I-A-M-M-O-S/AVA/CAD/KiCad/AVA/FAB/PDF/AVA-B_Cu.png

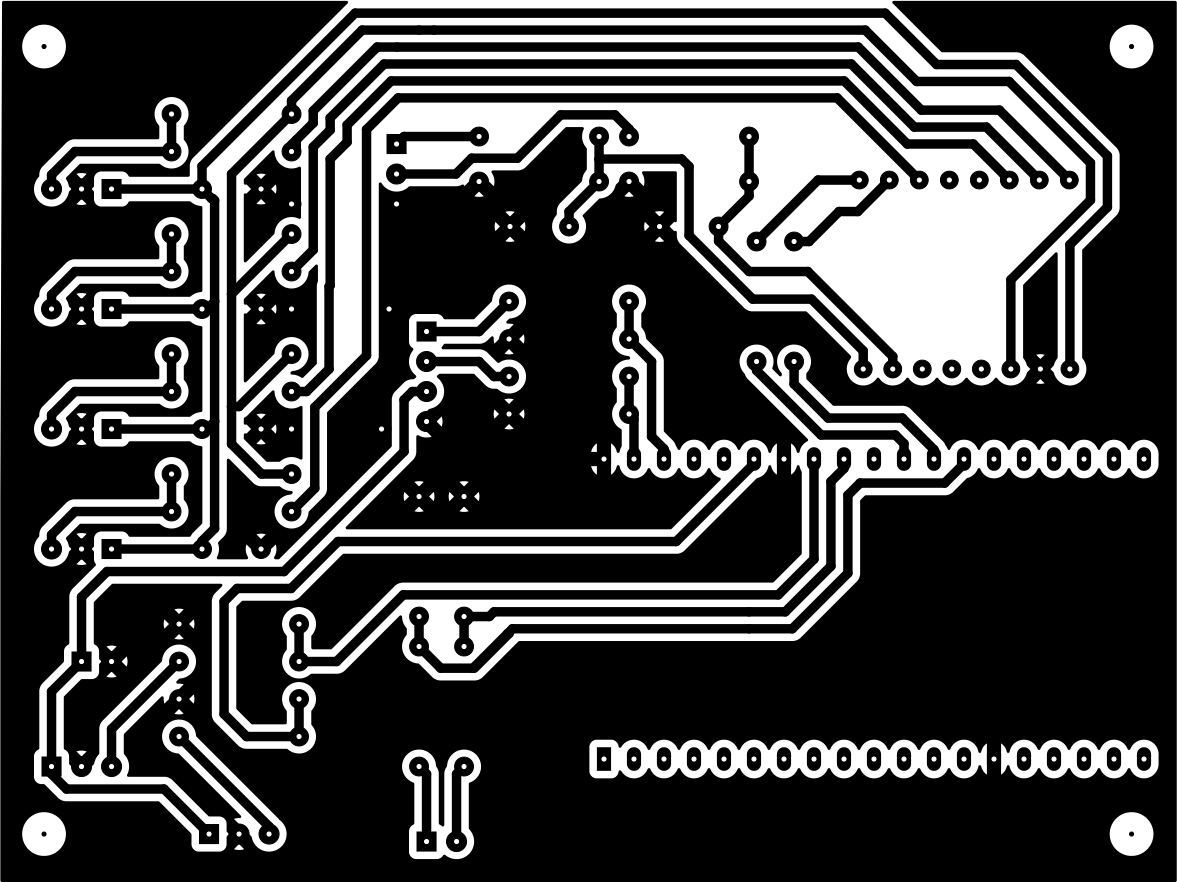
CAD/KiCad/AVA/FAB/PDF/AVA-B_Cu.png
