I-A-M-M-O-S/AVA/CAD/KiCad/AVA/FAB/SVG/AVA-F_Cu.png

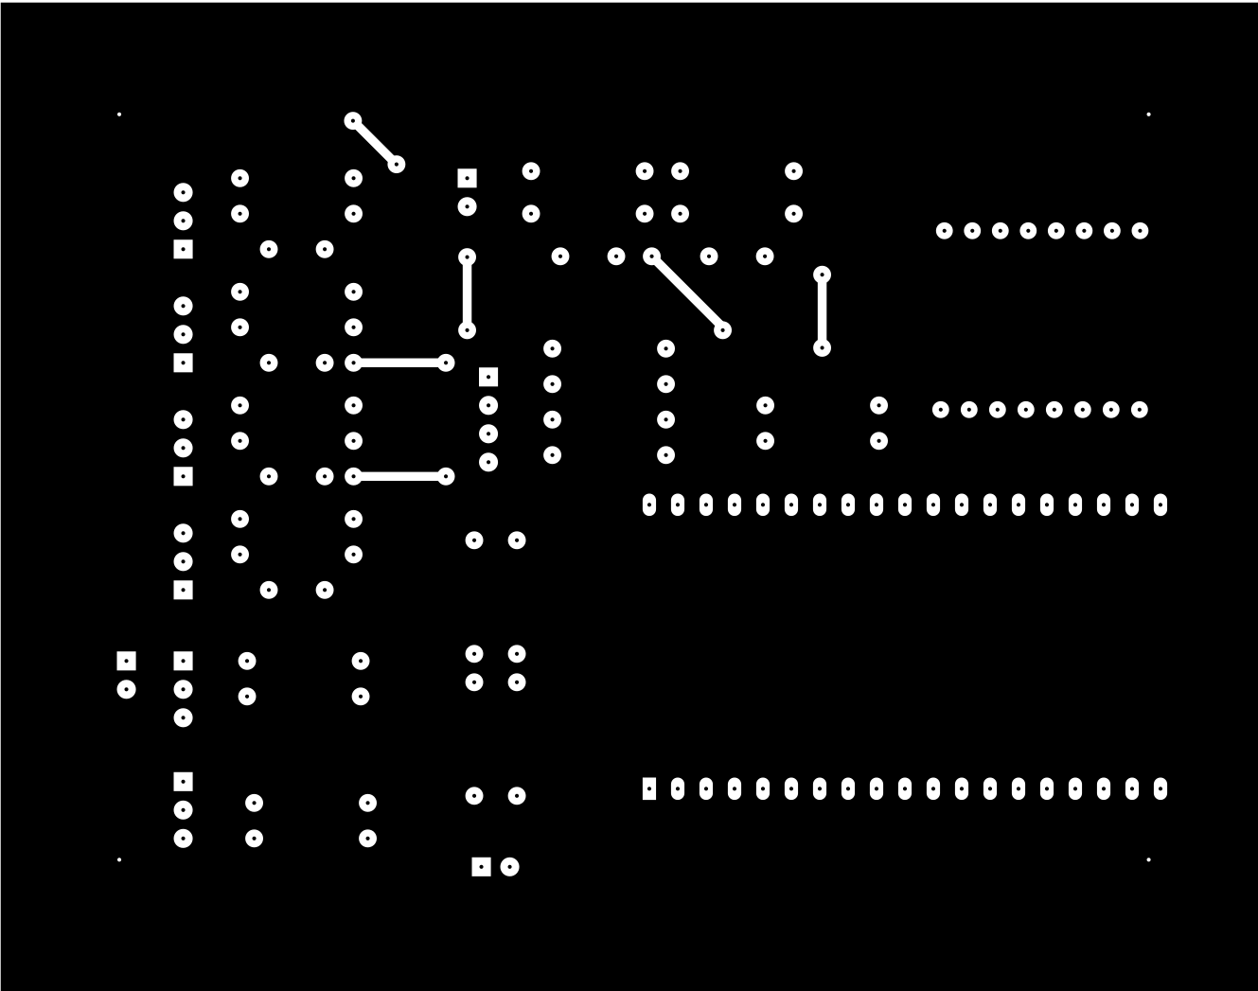
CAD/KiCad/AVA/FAB/SVG/AVA-F_Cu.png
