I-A-M-M-O-S/AVA/DOC/INTERNAL/MBSE/New Package/New_Diagram.png

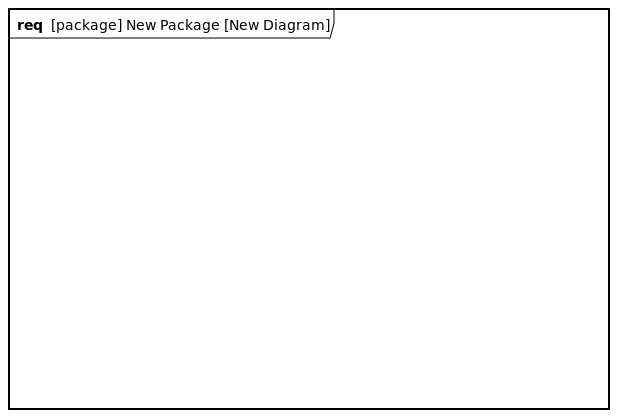
DOC/INTERNAL/MBSE/New Package/New_Diagram.png
