I-A-M-M-O-S/AVA/CAD/KiCad/AVA/FAB/PDF/PRINT.png

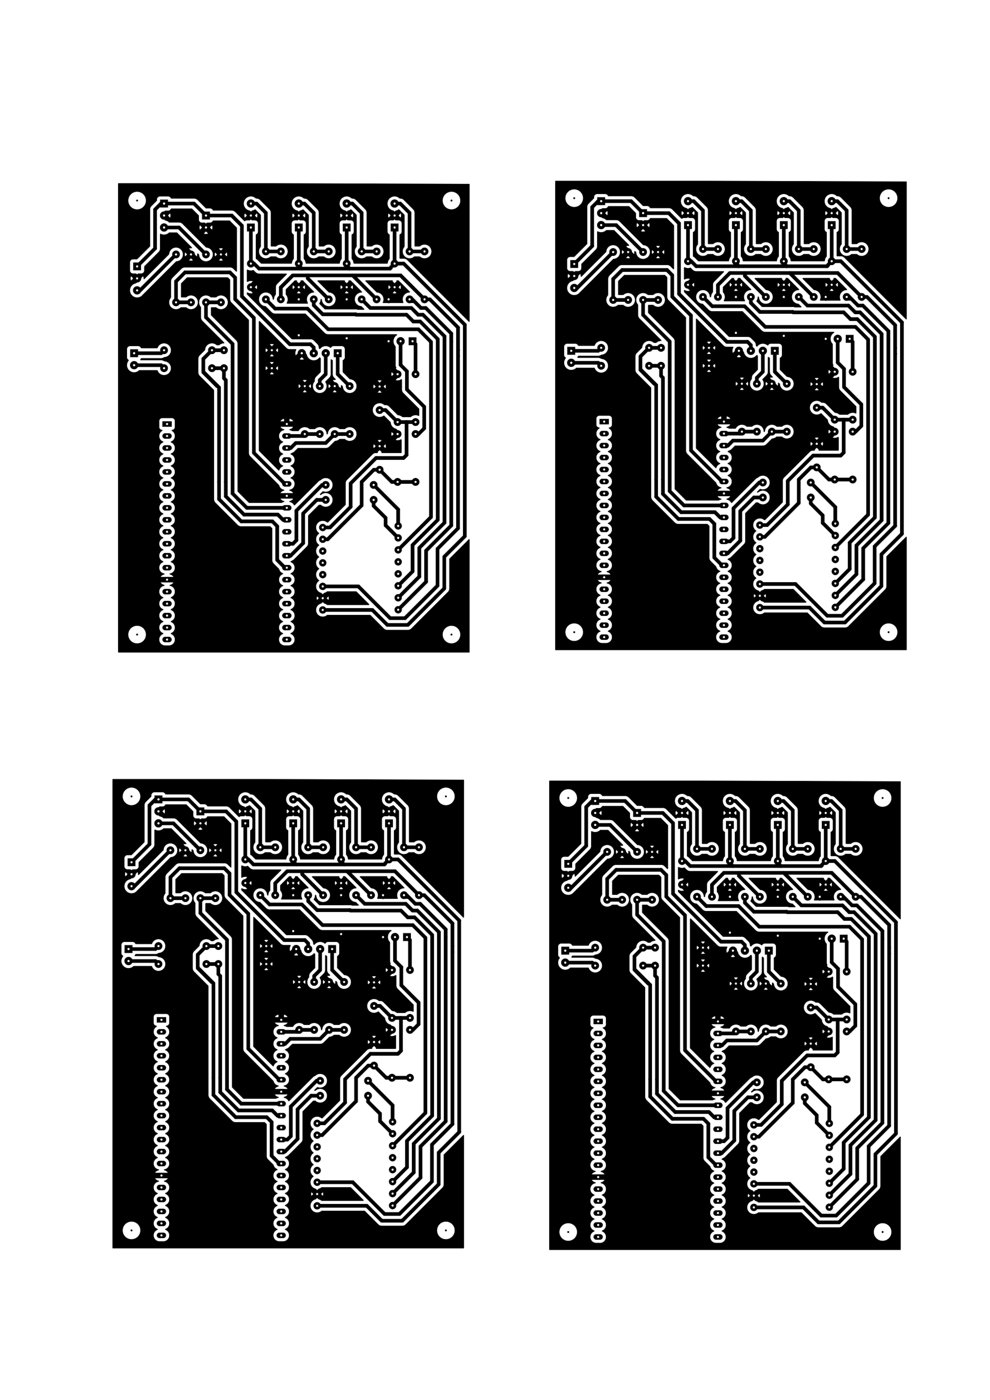
CAD/KiCad/AVA/FAB/PDF/PRINT.png
