I-A-M-M-O-S/AVA/CAD/KiCad/AVA/PRINT.png

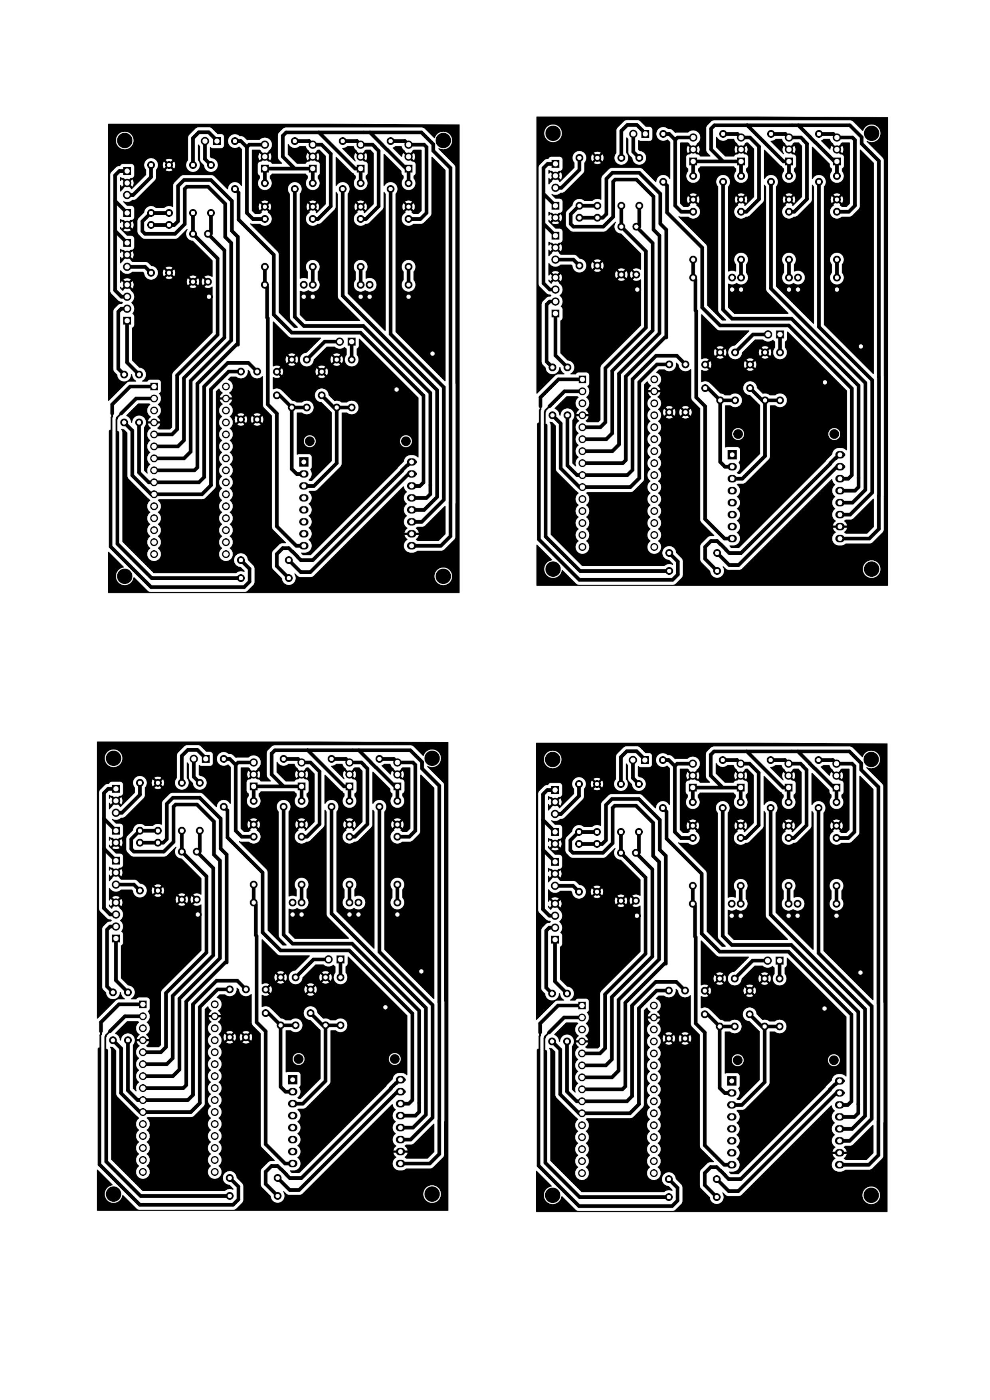
CAD/KiCad/AVA/PRINT.png
