I-A-M-M-O-S/AVA/CAD/KiCad/AVA/FAB/PDF/AVA-F_Silkscreen.pdf

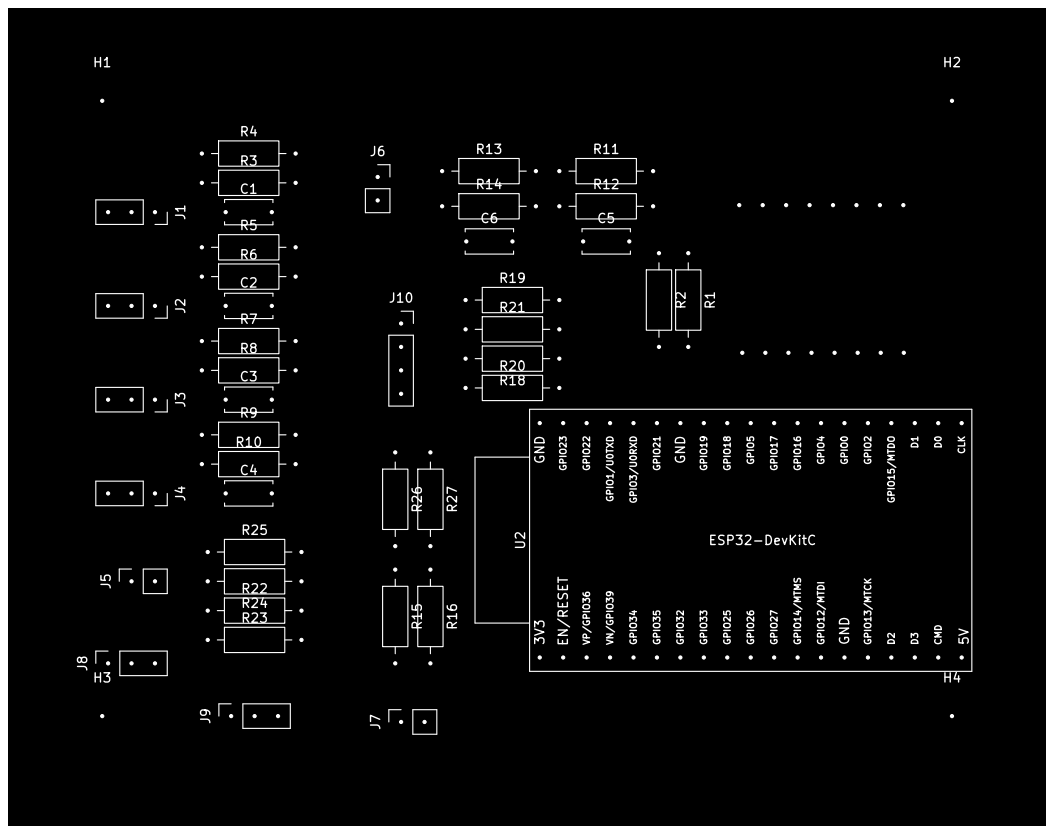
[picture p12: page 1]

R27 R3R7R25 J5 C6 R24 U2ESP32-DevKitC GND 3V3 EN/RESET GPIO23 GPIO22 VP/GPIO36 GPIO1/U0TXD VN/GPIO39 GPIO3/U0RXD GPIO34 GPIO21 GPIO35 GND GPIO32 GPIO19 GPIO33 GPIO18 GPIO25 GPIO5 GPIO26 GPIO17 GPIO27 GPIO16 GPIO14/MTMS GPIO4 GPIO12/MTDI GPIO0 GND GPIO2 GPIO13/MTCK GPIO15/MTDO D2 D1 D3 D0 CMD CLK 5V
